ryankenney/TiltLightBox/TiltLightBoxPin/core_logic/tilt_light_box.h

#ifndef COLOR_GENERATOR_INCLUDED
#define COLOR_GENERATOR_INCLUDED

#include <stdlib.h>
#include <limits.h>
#include "color_phase.h"
#include "color_alg_purple_calm.h"
#include "color_alg_disco.h"
#include "color_alg_off.h"
#include "color_alg_x.h"

// TODO [rkenney]: Remove debug
// #include <stdio.h>

#define DELAY_MILLIS 10;
#define COLOR_INCREMENT 4;

#define COLOR_ALG__NOOP 0
#define COLOR_ALG__PURPLE_CALM 1
#define COLOR_ALG__DISCO 2
#define COLOR_ALG__OFF 3
#define COLOR_ALG__A 4
#define COLOR_ALG__B 5
#define COLOR_ALG__C 6
#define COLOR_ALG__D 7

#define BOX_STATE__UPRIGHT 100
#define BOX_STATE__TILTING 101
#define BOX_STATE__TILTED 102

#ifdef __cplusplus
extern "C" {
#endif

typedef struct TILT_BOX {
	unsigned char startColor[3];
	unsigned char endColor[3];
	unsigned long transitionStartTime;
	unsigned long transitionDuration;
	unsigned char boxState;
	int colorAlg;
	PurpleCalmAlgState purpleCalmAlgState;
	DiscoAlgState discoAlgState;
	OffAlgState offAlgState;
	XAlgState xAlgState;
	/**
	 * Whether the box was tilted last cycle
	 */
	bool wasTilted;
} TiltBox;

/**
 * Returns the color of that box for the current time, given the box's state
 */
void getColor(TiltBox *box, unsigned char *result);

/**
 * An incrementing milliseconds clock time. The rollover value can obtained from ULONG_MAX (limits.h).
 * This is intended to mirror the millis() method provided by Arduino.
 */
unsigned long currentMillis();

/**
 * Sets the implementation of currentMillis()
 */
void setCurrentMillisFunc(unsigned long (*func)());

/**
 * Generates a random number greater than or equal to the provided
 * low value and less than the provided high value.
 */
unsigned long randomValue(int low, int high);

/**
 * Sets the implementation of randomValue()
 */
void setRandomValueFunc(int (*func)(int,int));

/**
 * A blocking sleep function. Similar to delay() for arduino.
 */
void sleepMillis(unsigned long millis);

/**
 * Sets the implementation of sleepMillis()
 */
void setSleepMillisFunc(void (*func)(unsigned long));

/**
 * Transmits an updated tilt state back to the central server
 */
void transmitTiltState(TiltBox *box, unsigned char state);

/**
 * Sets the implementation of transmitTiltState()
 */
void setTransmitTiltStateFunc(void (*func)(TiltBox *box, unsigned char boxState));

/**
 * Reads any theme change request from the central server.
 * Returns COLOR_ALG__NOOP if nothing was read (trasmitted).
 */
unsigned char receiveThemeChange(TiltBox *box);

/**
 * Sets the implementation of receiveThemeChange()
 */
void setReceiveThemeChangeFunc(unsigned char (*func)(TiltBox *box));

/**
 * Writes the specified color to the local LEDs
 */
void writeVisibleColor(TiltBox *box, unsigned char r, unsigned char g, unsigned char b);

/**
 * Sets the implementation of writeVisibleColor()
 */
void setWriteVisibleColorFunc(void (*func)(TiltBox *box, unsigned char r, unsigned char g, unsigned char b));

/**
 * Returns true iff the box is tilted in one or more directions
 */
bool tiltSensorIsActive(TiltBox *box);

/**
 * Sets the implementation of tiltSensorActive()
 */
void setTileSensorIsActiveFunc(bool (*func)(TiltBox *box));

/**
 * Mollocs and initializes a tilt light box object
 */
TiltBox * createTiltBox();

/**
 * Runs one cycle of the pimary logic
 */
void runCycle(TiltBox *box);

#ifdef __cplusplus
}
#endif

#endif
